sdrum01/dubsiren_rp2040/CAD/CAM/Settings_Fräser.png

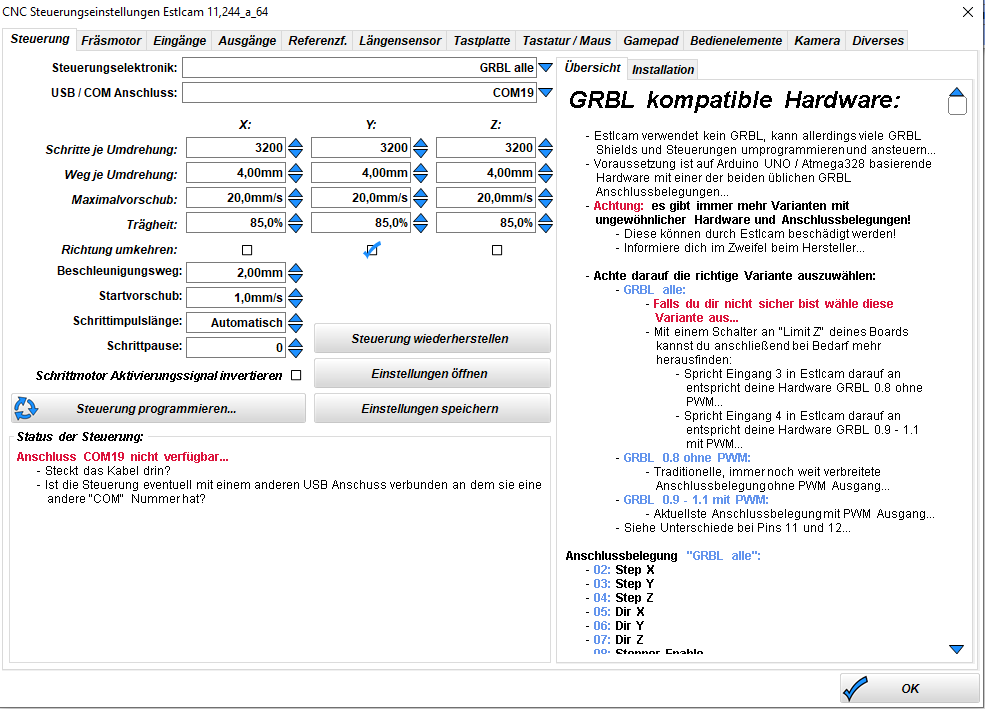
CAD/CAM/Settings_Fräser.png
