sdrum01/dubsiren_rp2040/CAD/CAM/Settings_Fräser_ref.png

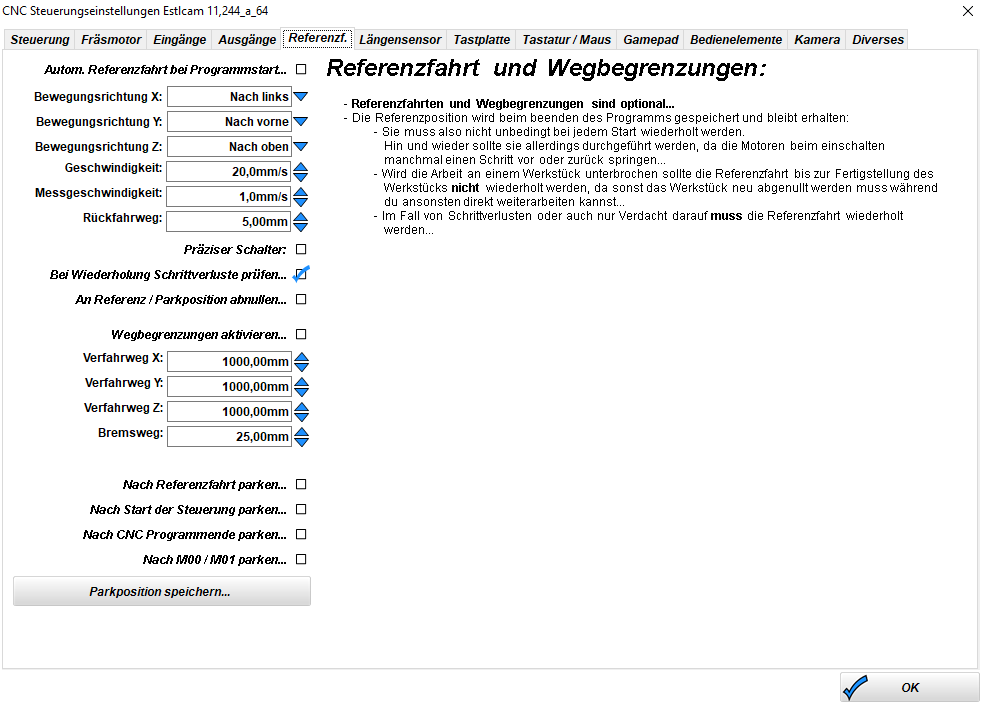
CAD/CAM/Settings_Fräser_ref.png
