sdrum01/dubsiren_rp2040/CAD/DXF/Front_DUBIY_mit_Beschriftung_buisnesscard.jpg

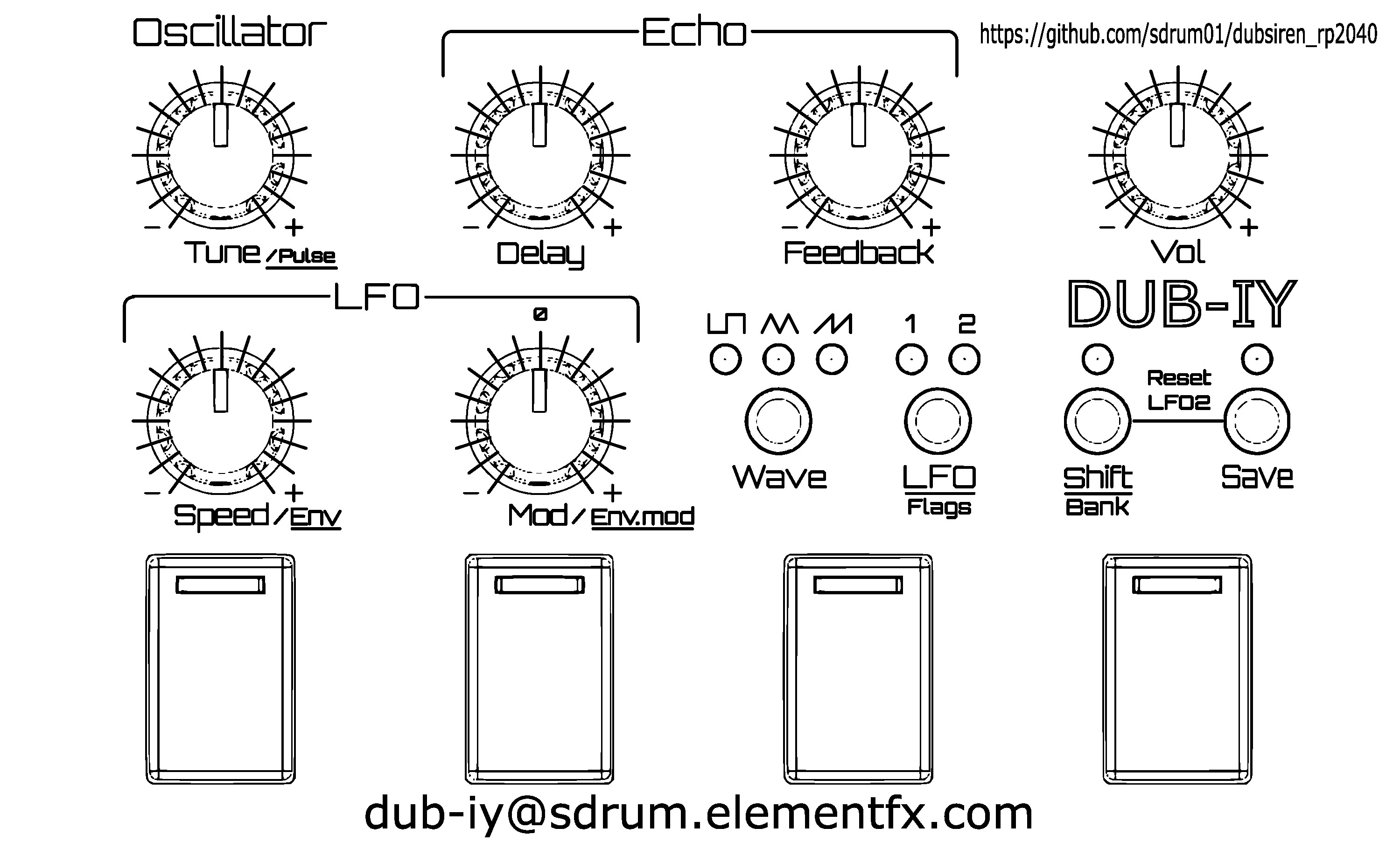
CAD/DXF/Front_DUBIY_mit_Beschriftung_buisnesscard.jpg
