sdrum01/dubsiren_rp2040/CAD/DXF/DIYBody - Frontplatte_EMS.dxf

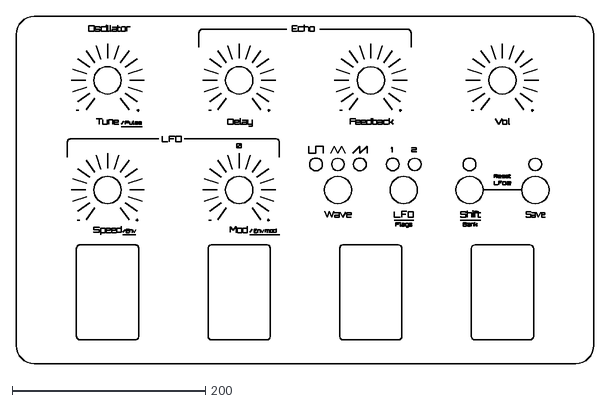
[picture p32: CAD file, 2024-12-12]
CAD/DXF/DIYBody - Frontplatte_EMS.dxf
597.2 x 359.1
