sdrum01/dubsiren_rp2040/CAD/STL/10/DIYStreifen_V10.1.stl

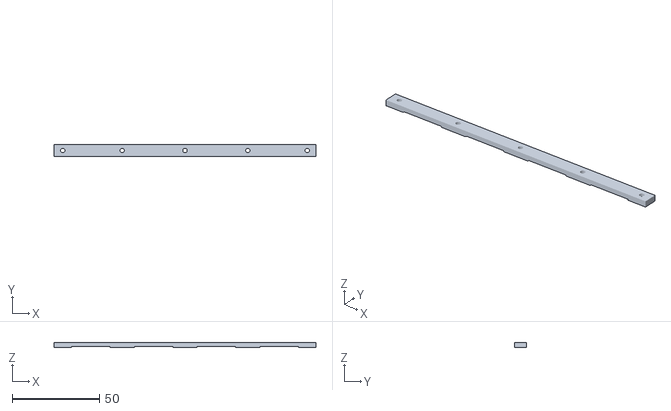
[picture p33: CAD file, 2024-12-03]
CAD/STL/10/DIYStreifen_V10.1.stl
150.0 x 7.00 x 3.00
