sdrum01/dubsiren_rp2040/CAD/STL/12/DIYBodyBottomSlim_V12.3.stl

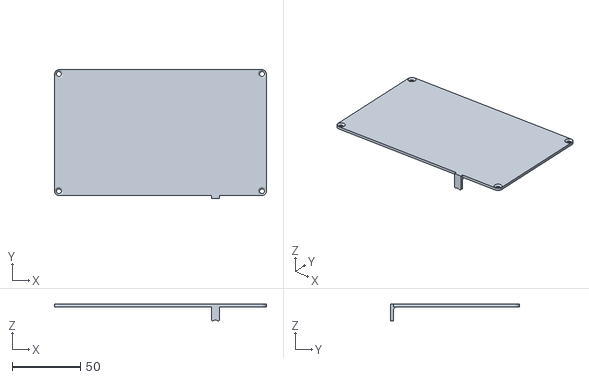
[picture p34: CAD file, 2025-01-31]
CAD/STL/12/DIYBodyBottomSlim_V12.3.stl
155.5 x 94.5 x 12.3
