sdrum01/dubsiren_rp2040/CAD/DXF/DIYBody - Frontplatte.dxf

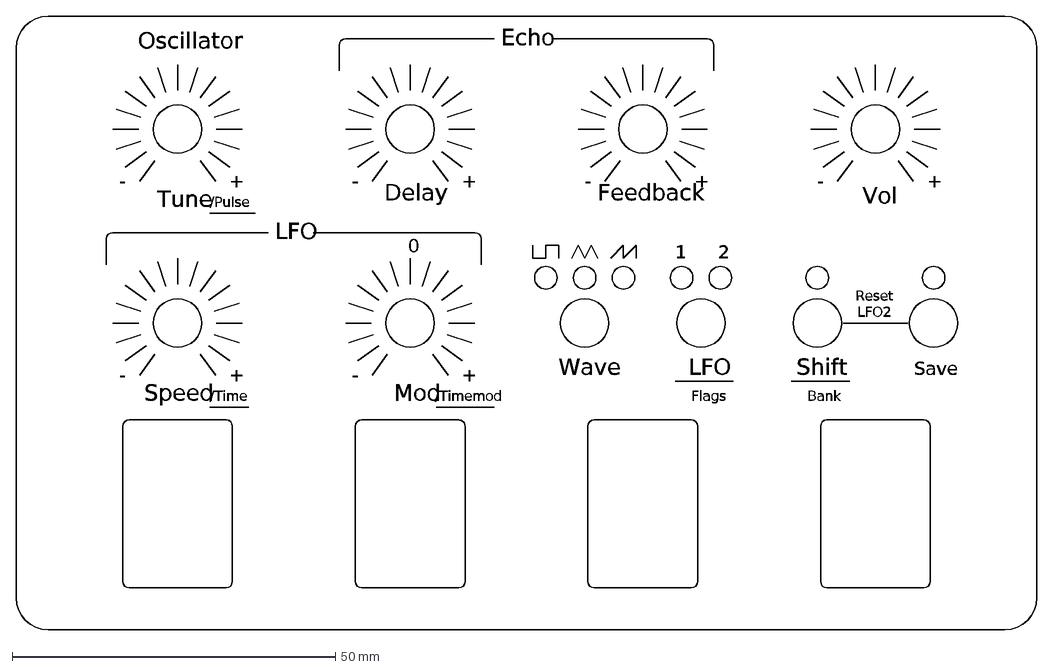
[picture p35: CAD file, 2024-12-08]
CAD/DXF/DIYBody - Frontplatte.dxf
-
+
0
2
1
Speed
Mod
/Time
/Timemod
Wave
LFO
Shift
Tune
Delay
Feedback
/Pulse
Bank
Save
Flags
Reset LFO2
Oscillator
Vol
Echo
