sdrum01/dubsiren_rp2040/CAD/STL/10/DIYKnob Fire - Inlay square.stl

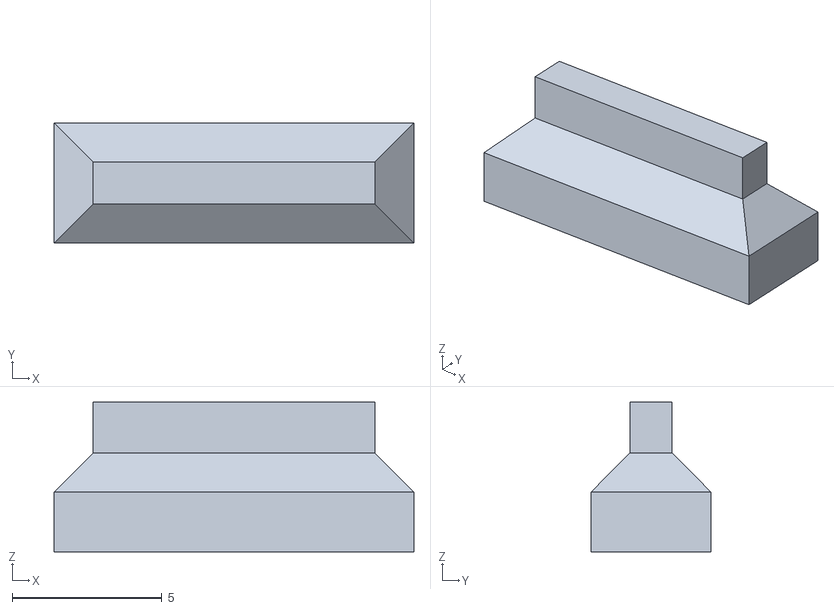
[picture p36: CAD file, 2024-12-02]
CAD/STL/10/DIYKnob Fire - Inlay square.stl
12.0 x 4.00 x 5.00
