sdrum01/dubsiren_rp2040/CAD/STL/12/DIYKnobFire - Inlay_V12.3.stl

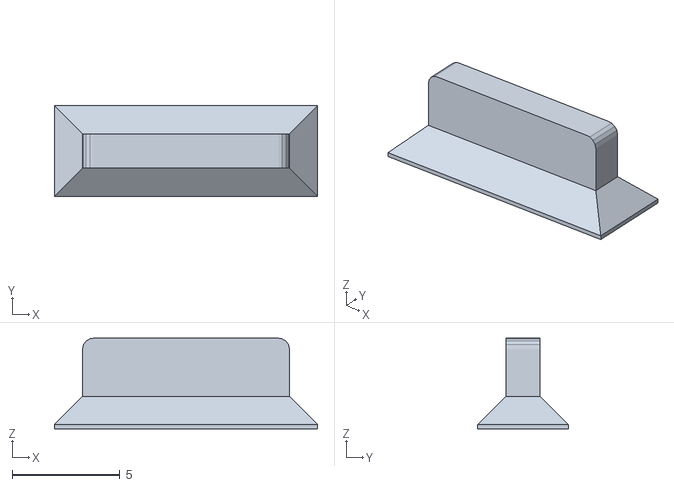
[picture p37: CAD file, 2025-01-31]
CAD/STL/12/DIYKnobFire - Inlay_V12.3.stl
12.2 x 4.20 x 4.20
