sdrum01/dubsiren_rp2040/CAD/STL/11/DIYDeckel_V11.4_5mm.stl

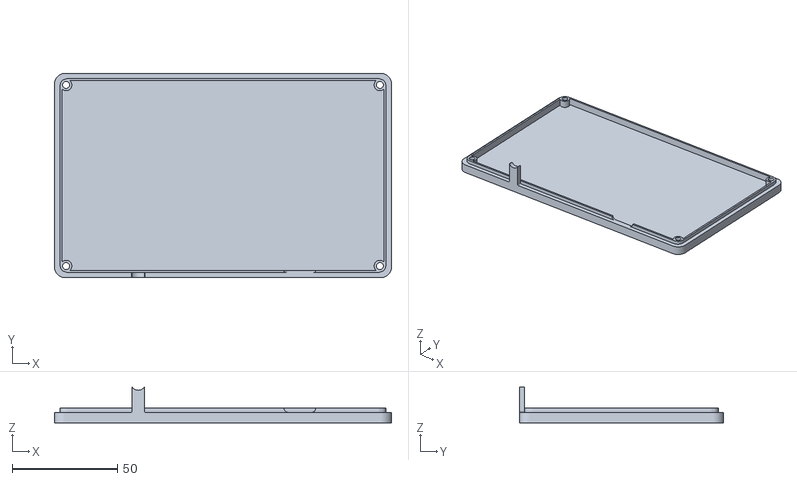
[picture p38: CAD file, 2024-12-12]
CAD/STL/11/DIYDeckel_V11.4_5mm.stl
160.0 x 97.0 x 17.0
