sdrum01/dubsiren_rp2040/CAD/STL/12/DIYKnobShift_V12.2_8mm.stl

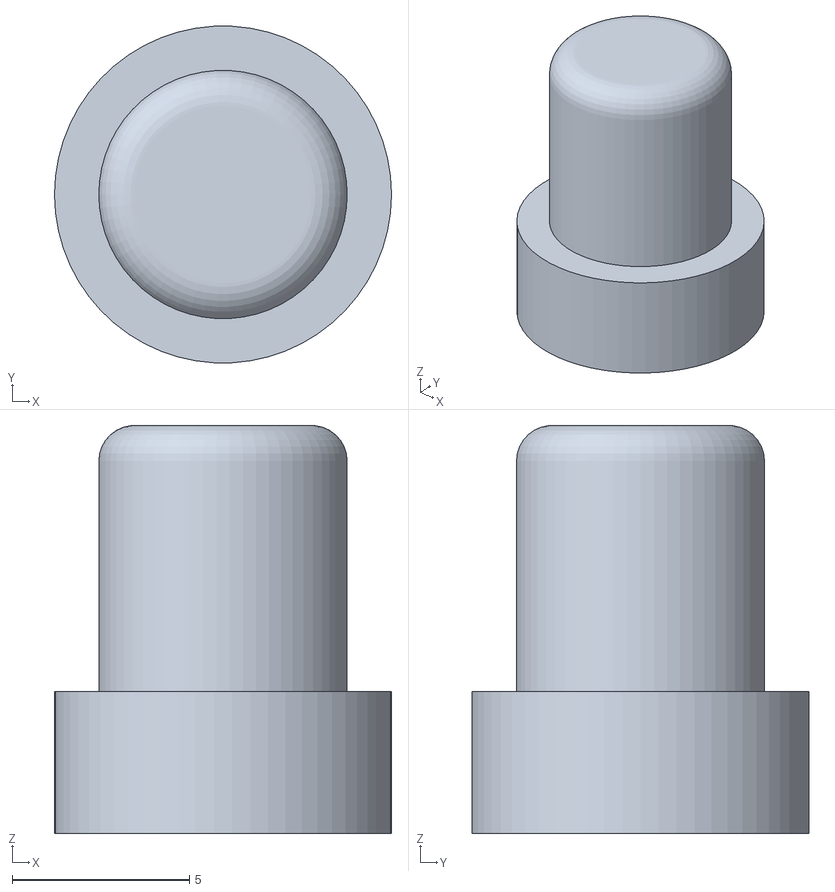
[picture p39: CAD file, 2025-01-07]
CAD/STL/12/DIYKnobShift_V12.2_8mm.stl
9.50 x 9.49 x 11.5
