sdrum01/dubsiren_rp2040/CAD/STL/11/DIYKnobFireStößel_V11.2.stl

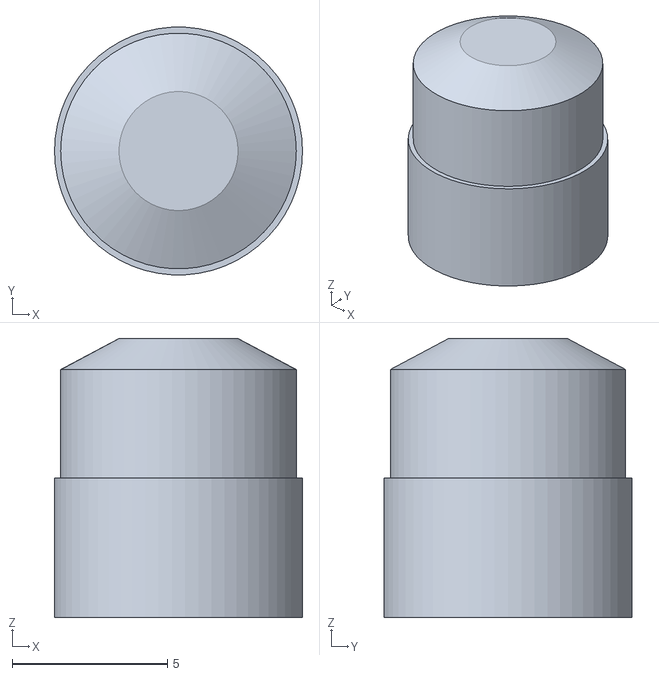
[picture p40: CAD file, 2024-12-12]
CAD/STL/11/DIYKnobFireStößel_V11.2.stl
8.00 x 7.99 x 9.00
