sdrum01/dubsiren_rp2040/CAD/STL/11/DIYDeckel_V11.4_15mm.stl

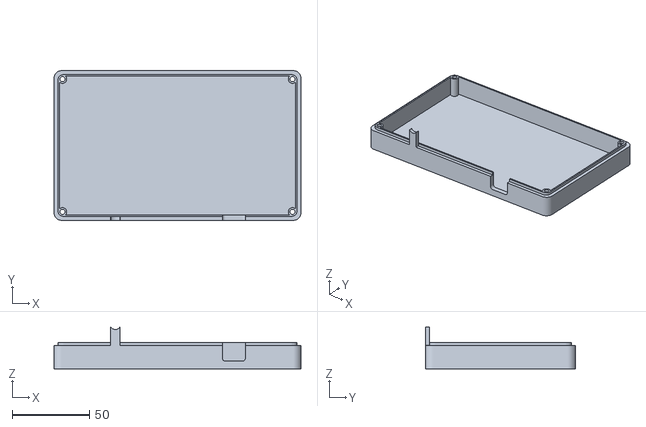
[picture p41: CAD file, 2024-12-12]
CAD/STL/11/DIYDeckel_V11.4_15mm.stl
160.0 x 97.0 x 27.0
