sdrum01/dubsiren_rp2040/CAD/STL/12/PotiKnob - Inlays_x10_V12.0.stl

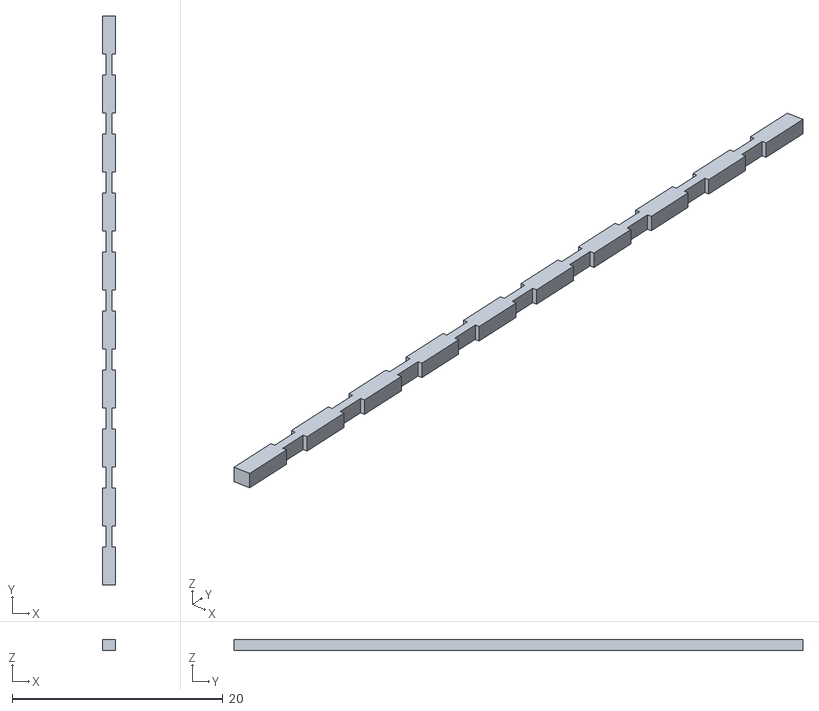
[picture p42: CAD file, 2025-01-06]
CAD/STL/12/PotiKnob - Inlays_x10_V12.0.stl
1.20 x 54.0 x 1.00
