sdrum01/dubsiren_rp2040/CAD/STL/11/DIYDeckel_V11.1_10mm.stl

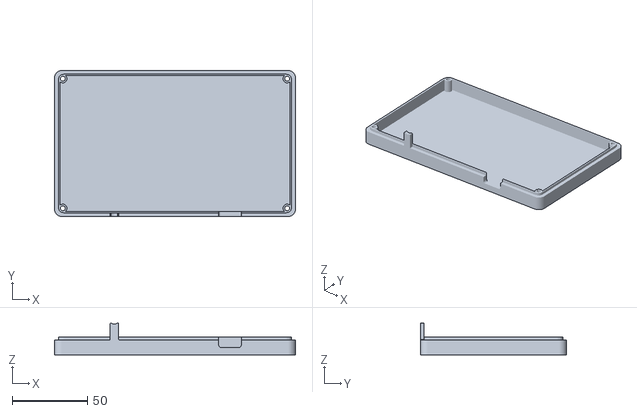
[picture p43: CAD file, 2024-12-09]
CAD/STL/11/DIYDeckel_V11.1_10mm.stl
160.0 x 97.0 x 21.2
